apct-2019/Onias/GainBlock_datasheet_ckt.PNG

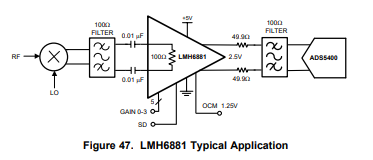
GainBlock_datasheet_ckt.PNG
