apct-2019/Onias/LNA_2d_layout.PNG

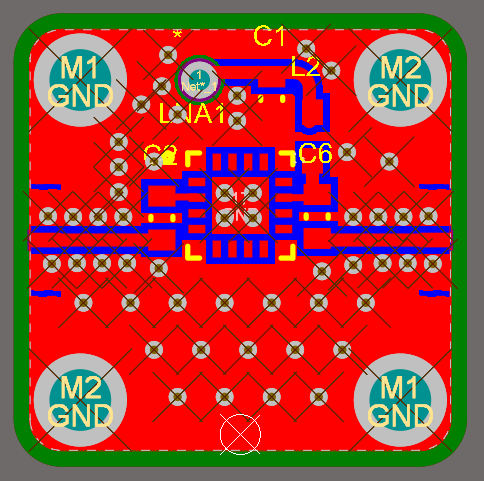
LNA_2d_layout.PNG
